ambariz/Splitix-MK1/assets/left_3d.png

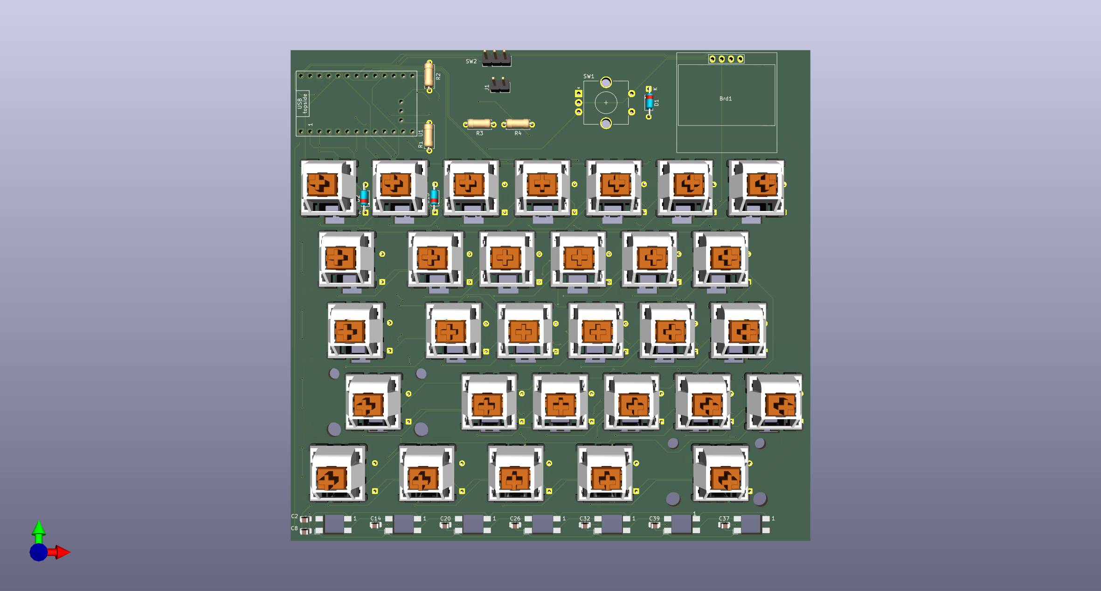
assets/left_3d.png
